varunsontakke80/Jal-Rakshak-Project-Arduino-UNO-Q/Images/Jal_Rakshak_Master_Node_Code_Flowchart.jpg

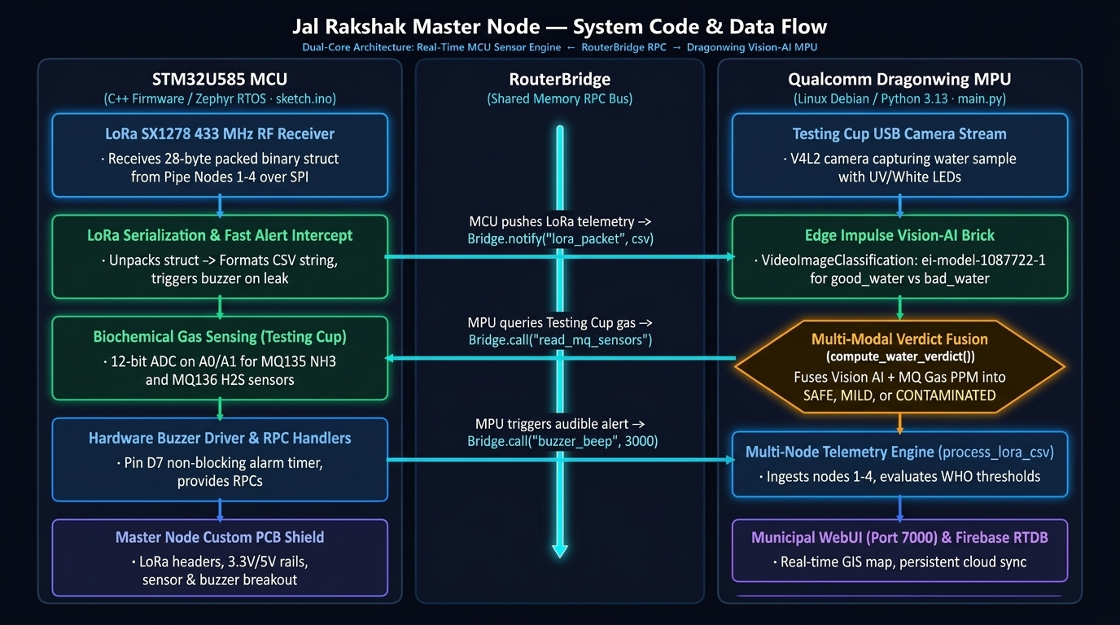
Images/Jal_Rakshak_Master_Node_Code_Flowchart.jpg
