varunsontakke80/Jal-Rakshak-Project-Arduino-UNO-Q/Images/JR1.jpeg

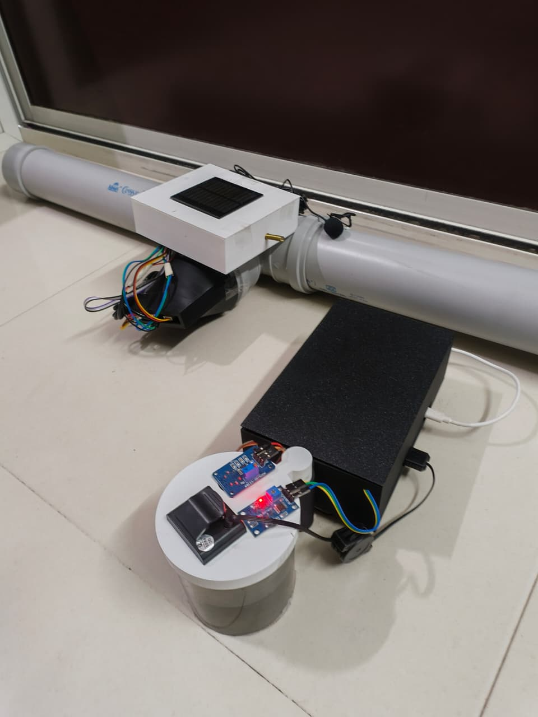
Images/JR1.jpeg
