varunsontakke80/Jal-Rakshak-Project-Arduino-UNO-Q/Images/JR2.jpeg

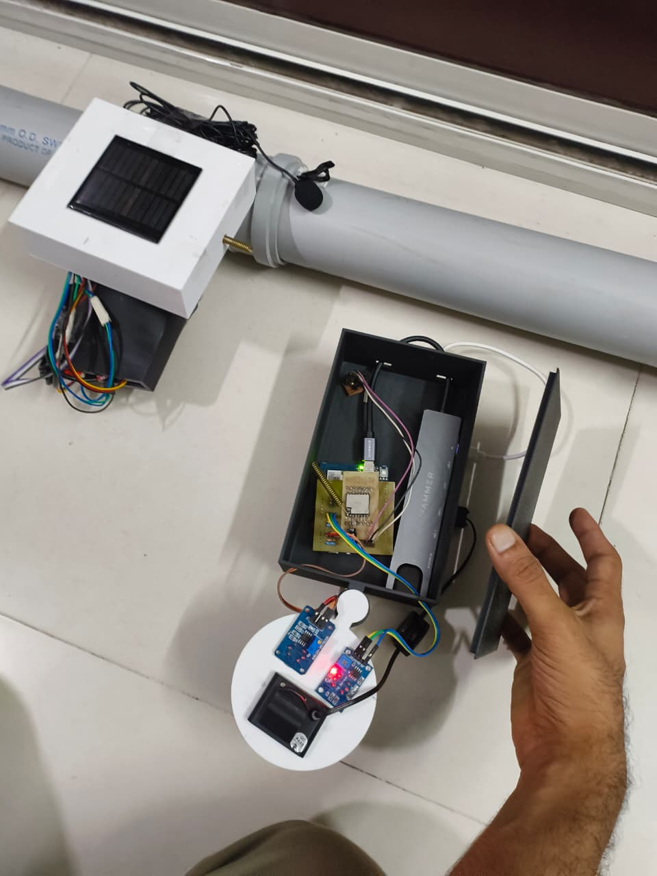
Images/JR2.jpeg
