varunsontakke80/Jal-Rakshak-Project-Arduino-UNO-Q/Images/JR3.jpeg

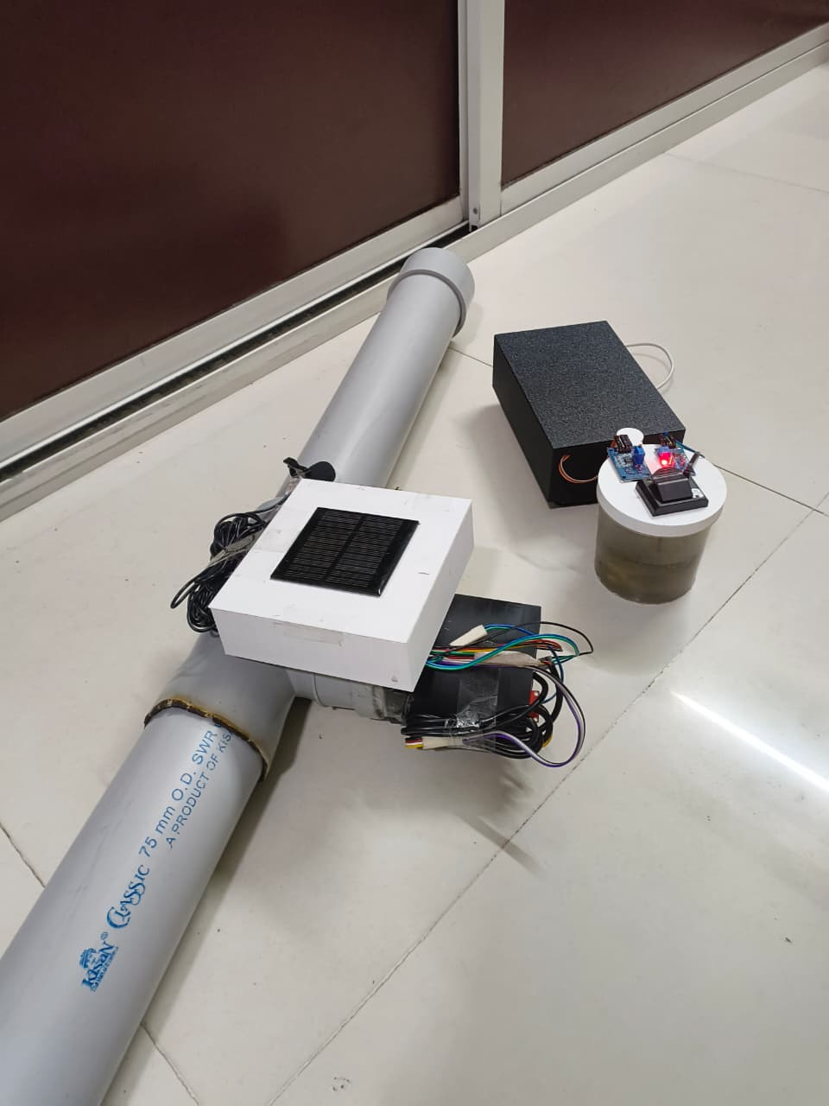
Images/JR3.jpeg
