varunsontakke80/Jal-Rakshak-Project-Arduino-UNO-Q/Images/JR4.jpeg

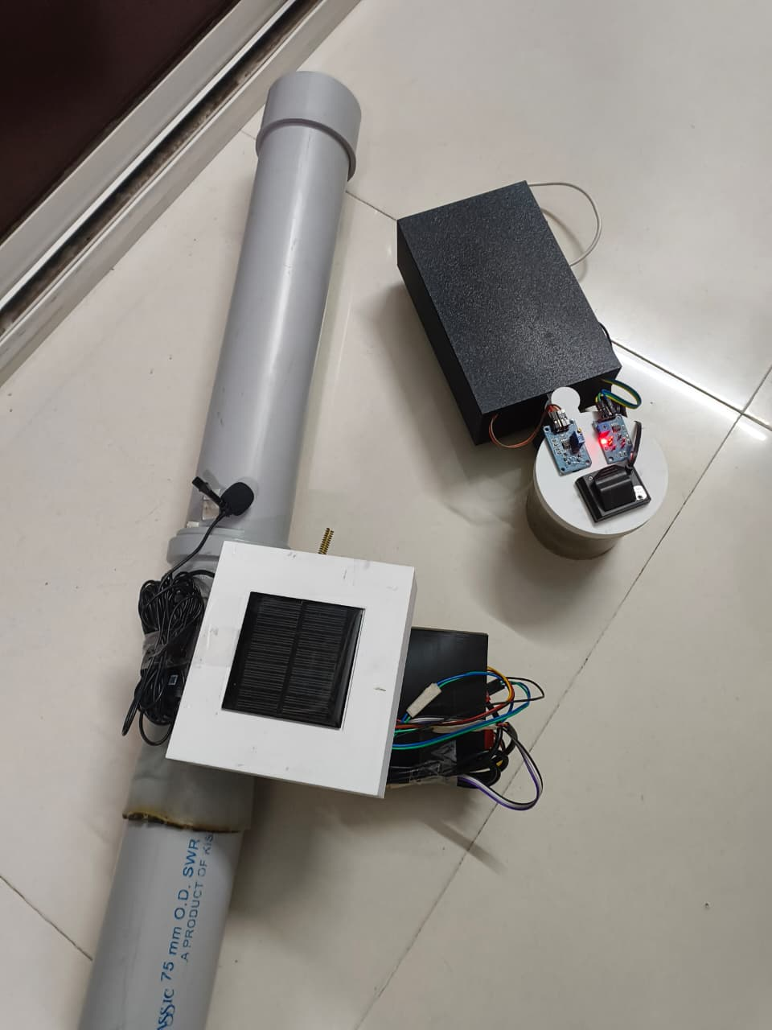
Images/JR4.jpeg
