varunsontakke80/Jal-Rakshak-Project-Arduino-UNO-Q/Images/JR5.jpeg

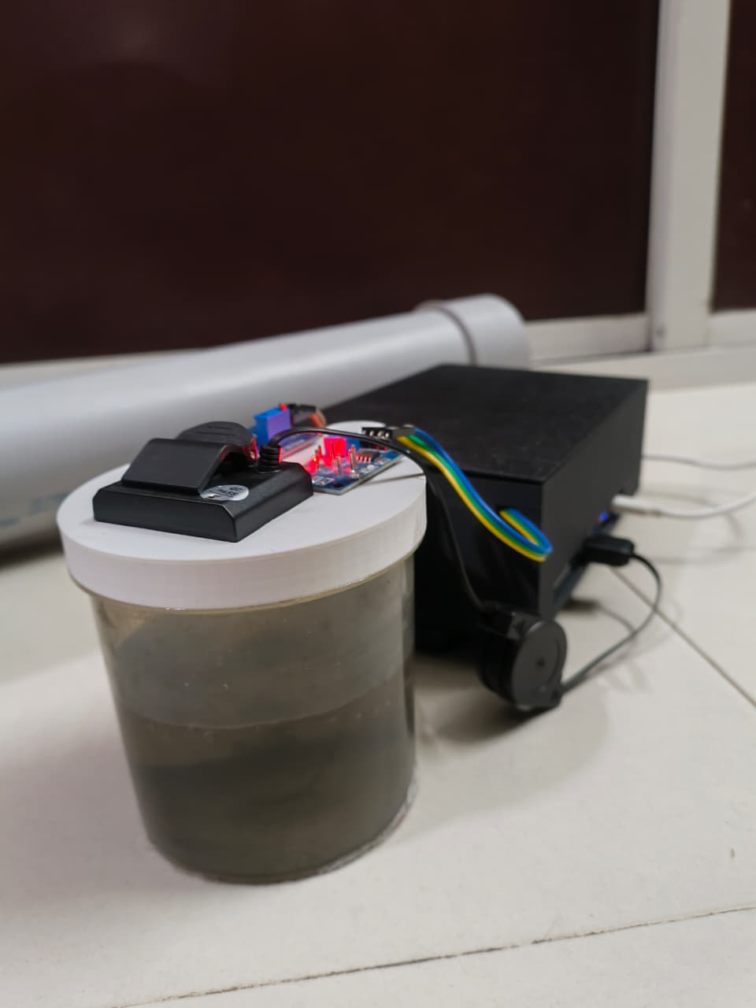
Images/JR5.jpeg
