varunsontakke80/Jal-Rakshak-Project-Arduino-UNO-Q/Images/JR6.jpeg

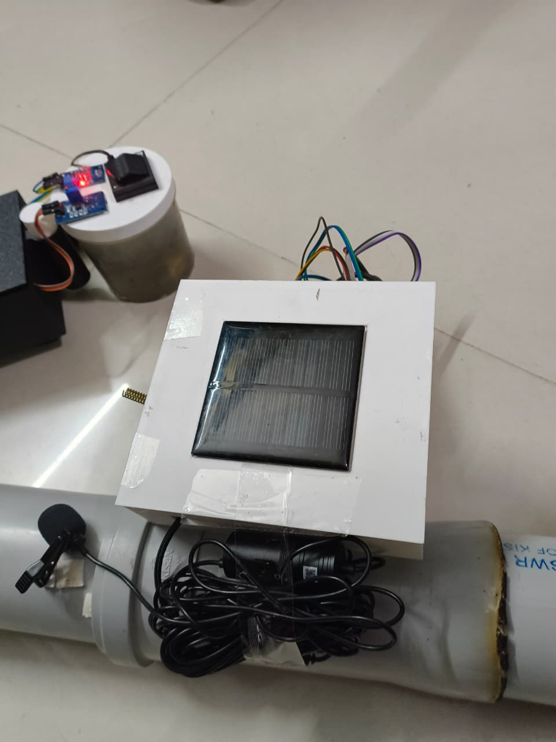
Images/JR6.jpeg
