varunsontakke80/Jal-Rakshak-Project-Arduino-UNO-Q/Images/JR7.jpeg

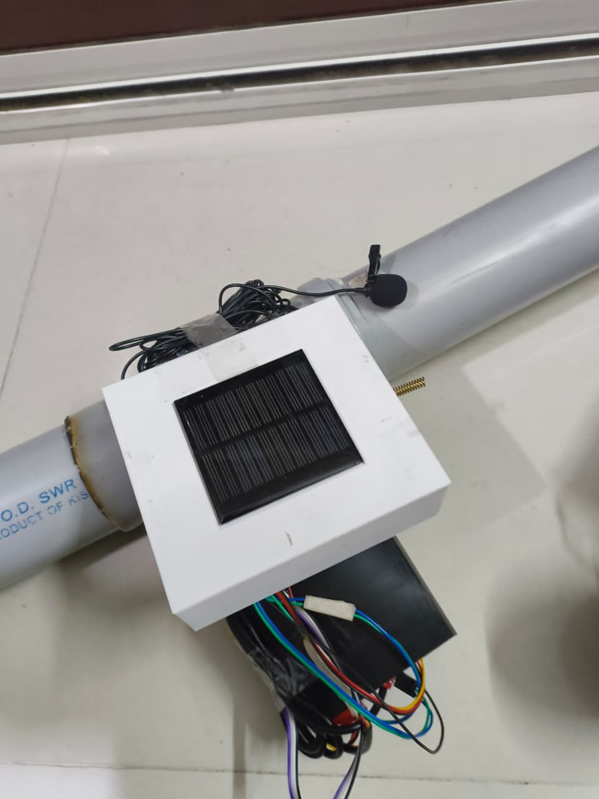
Images/JR7.jpeg
