varunsontakke80/Jal-Rakshak-Project-Arduino-UNO-Q/Images/JR8.jpeg

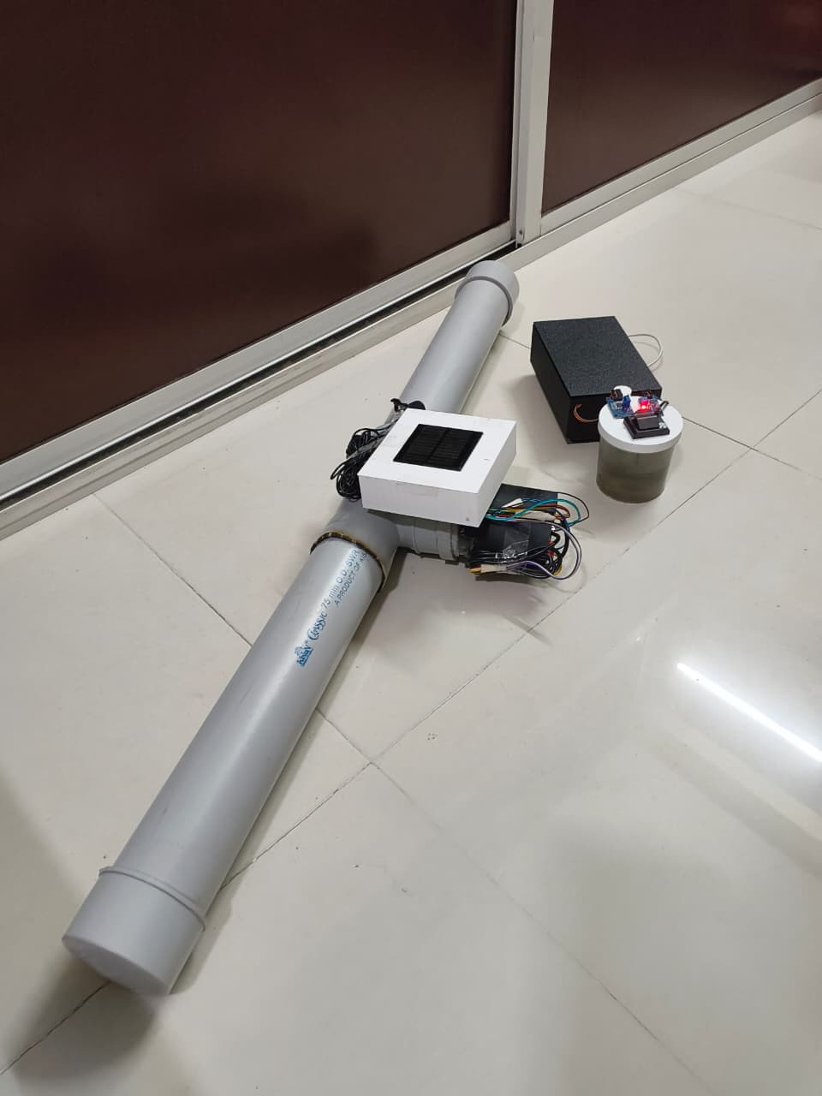
Images/JR8.jpeg
