varunsontakke80/Jal-Rakshak-Project-Arduino-UNO-Q/Images/Usb C hub.png

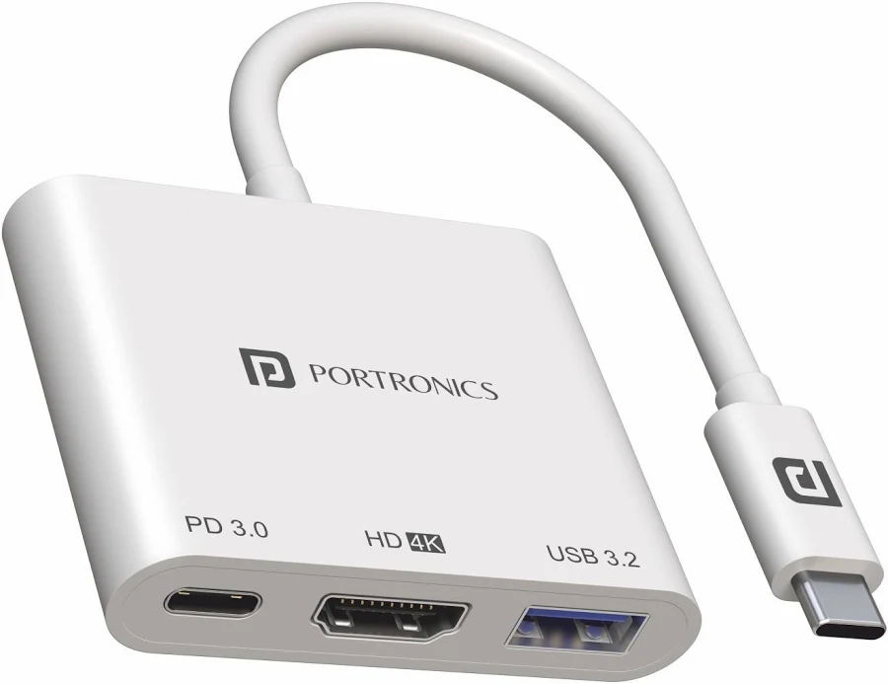
Images/Usb C hub.png
