varunsontakke80/Jal-Rakshak-Project-Arduino-UNO-Q/Images/USBc Mic.png

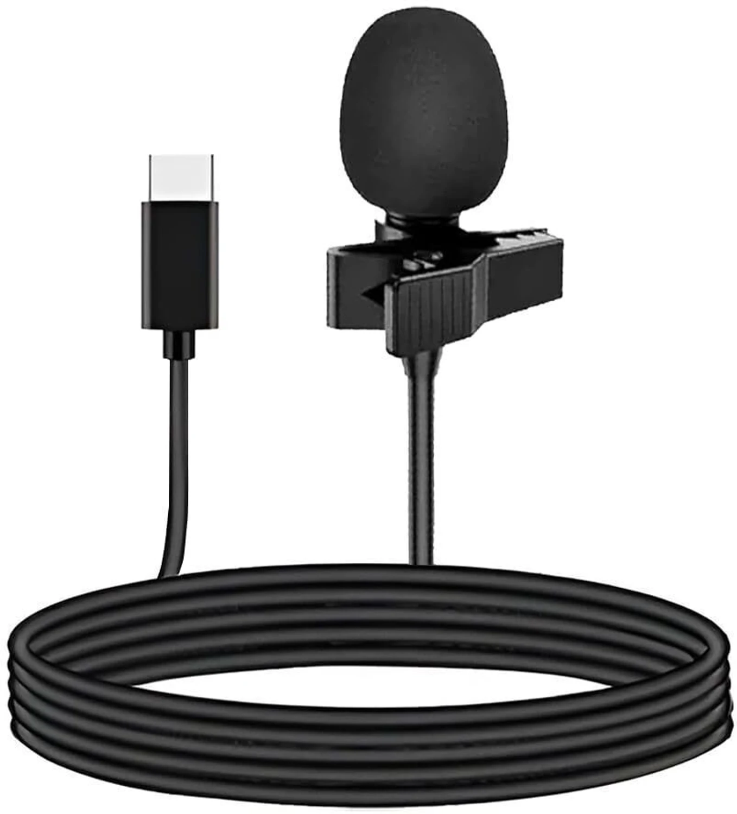
Images/USBc Mic.png
