varunsontakke80/Jal-Rakshak-Project-Arduino-UNO-Q/Master Node/CAD Files/Master Node CAD image.png

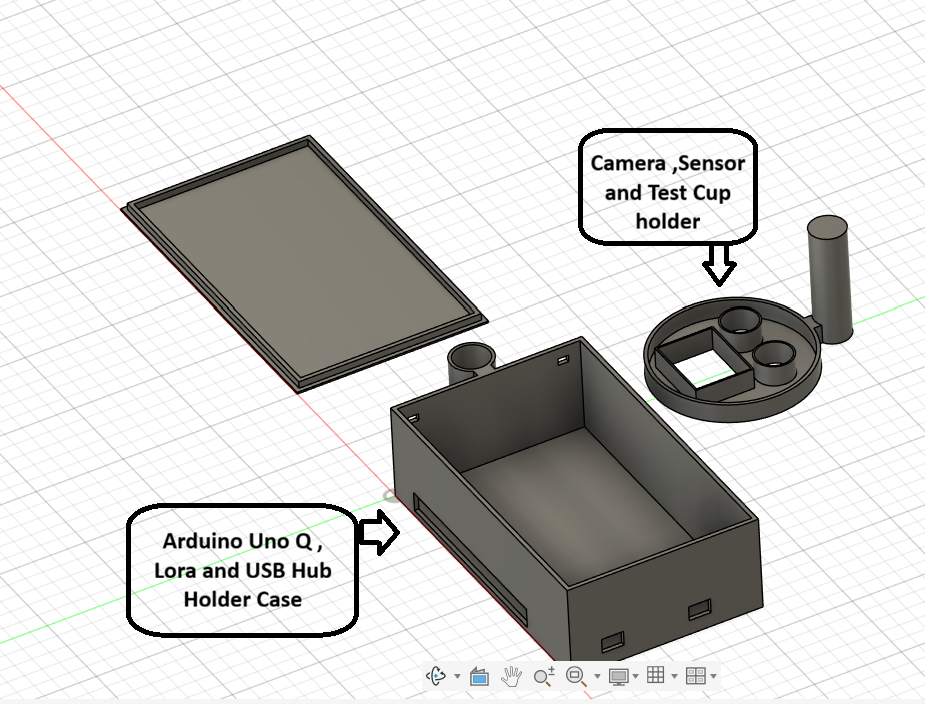
Master Node/CAD Files/Master Node CAD image.png
