varunsontakke80/Jal-Rakshak-Project-Arduino-UNO-Q/Master Node/CAD Files/Slicing SS1.png

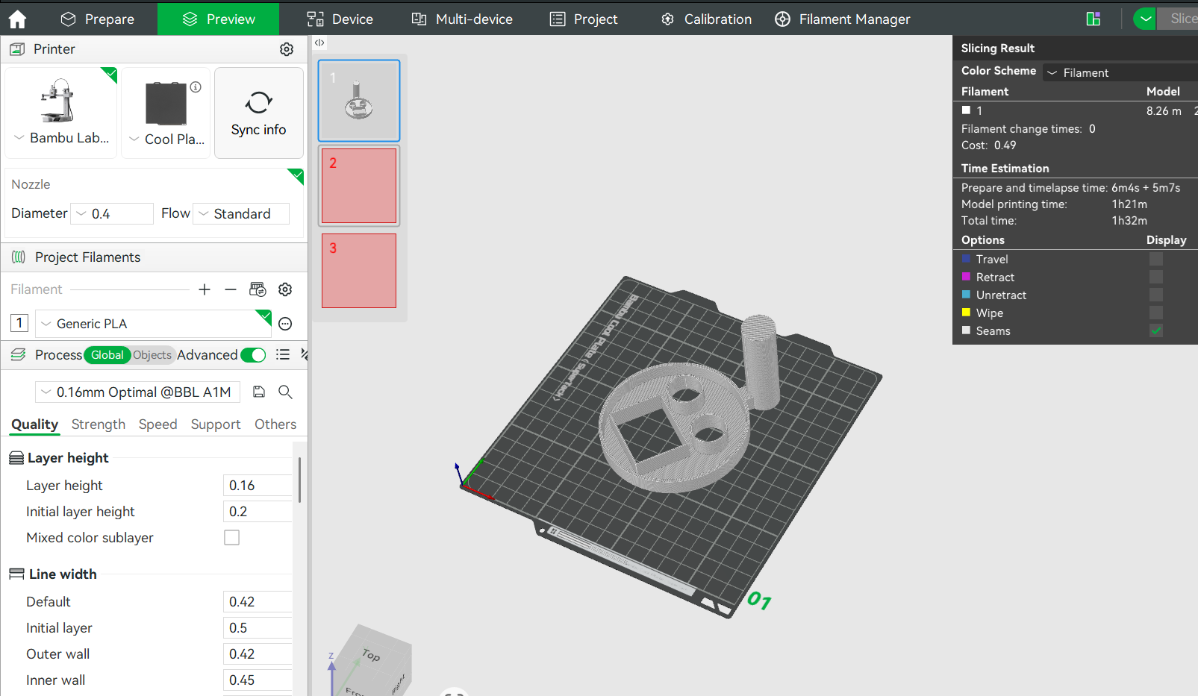
Master Node/CAD Files/Slicing SS1.png
