varunsontakke80/Jal-Rakshak-Project-Arduino-UNO-Q/Master Node/CAD Files/Slicing SS2.png

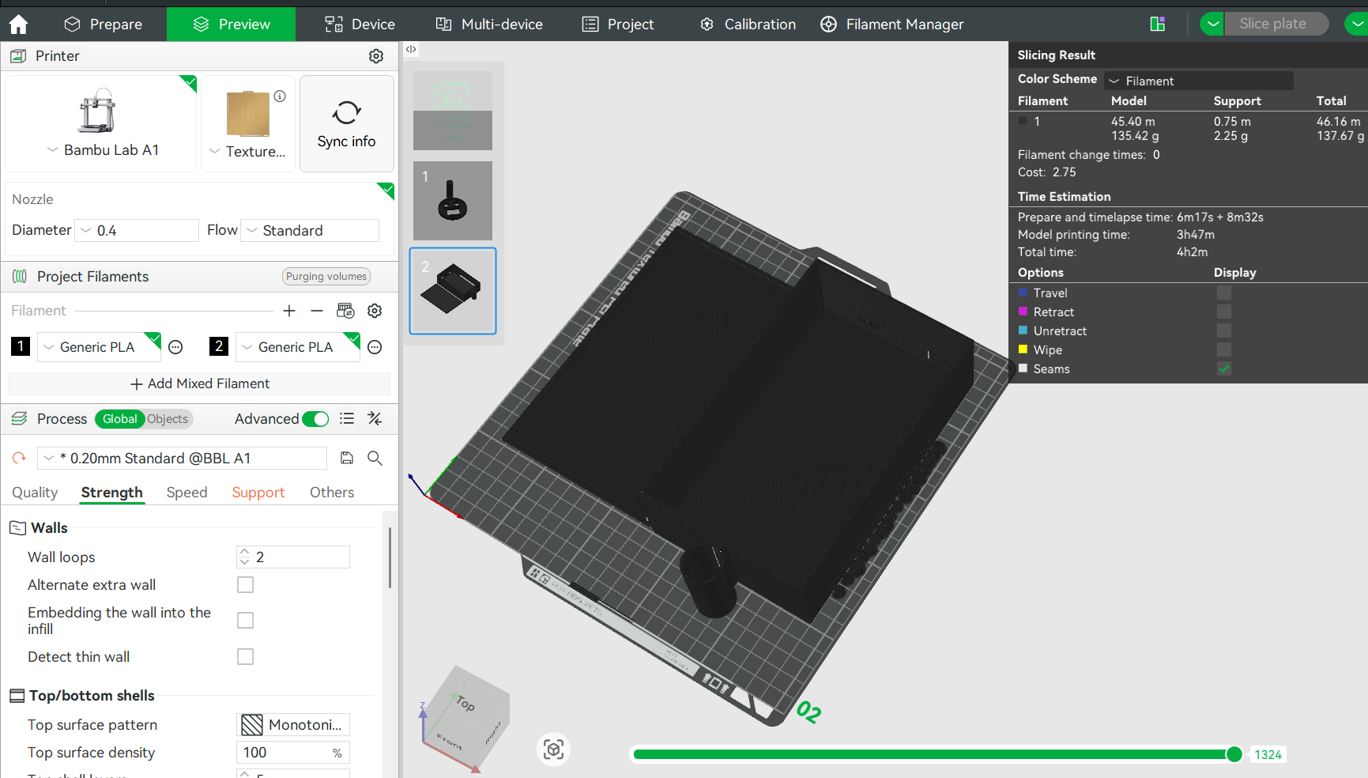
Master Node/CAD Files/Slicing SS2.png
