varunsontakke80/Jal-Rakshak-Project-Arduino-UNO-Q/Master Node/PCB Files/PCB_Jal Rakshak Master node.png

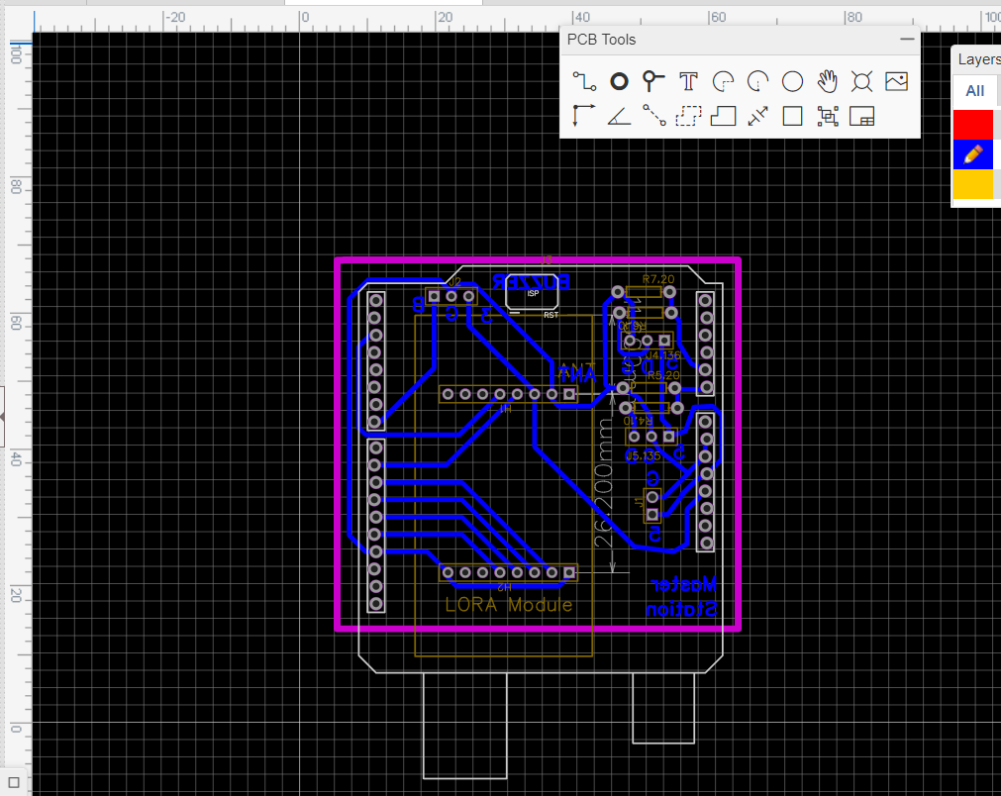
Master Node/PCB Files/PCB_Jal Rakshak Master node.png
