varunsontakke80/Jal-Rakshak-Project-Arduino-UNO-Q/Master Node/PCB Files/Schematic_Jal-Rakshak-Master-Node_2026-09-11.png

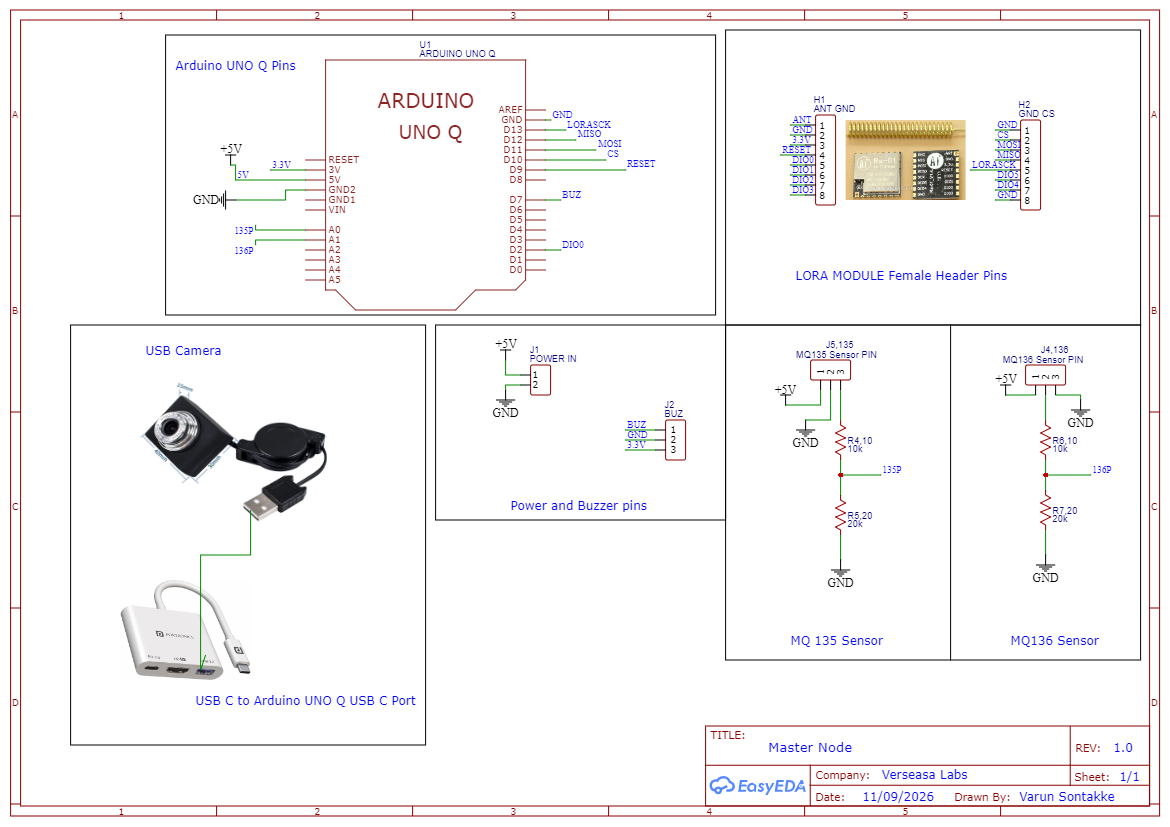
Master Node/PCB Files/Schematic_Jal-Rakshak-Master-Node_2026-09-11.png
