varunsontakke80/Jal-Rakshak-Project-Arduino-UNO-Q/Pipe Node/CAD Files/Pipe node Case .png

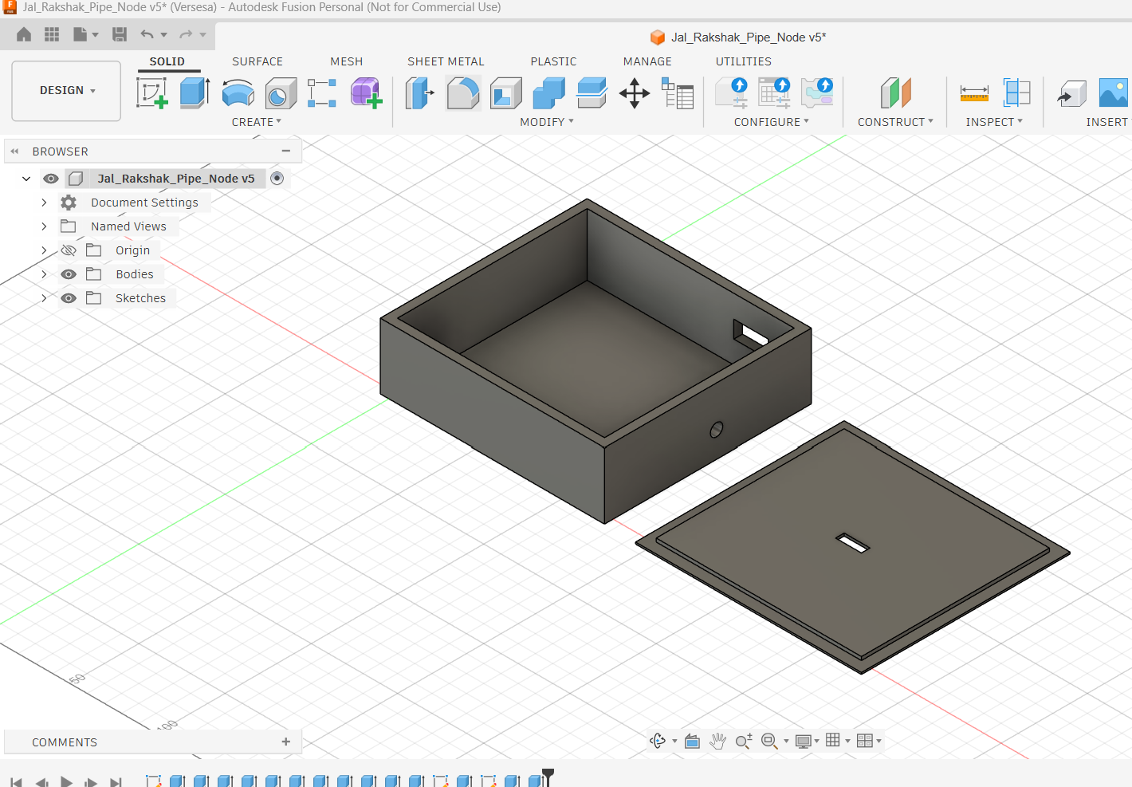
Pipe Node/CAD Files/Pipe node Case .png
