varunsontakke80/Jal-Rakshak-Project-Arduino-UNO-Q/Pipe Node/CAD Files/Pipe Node Sensor Case.png

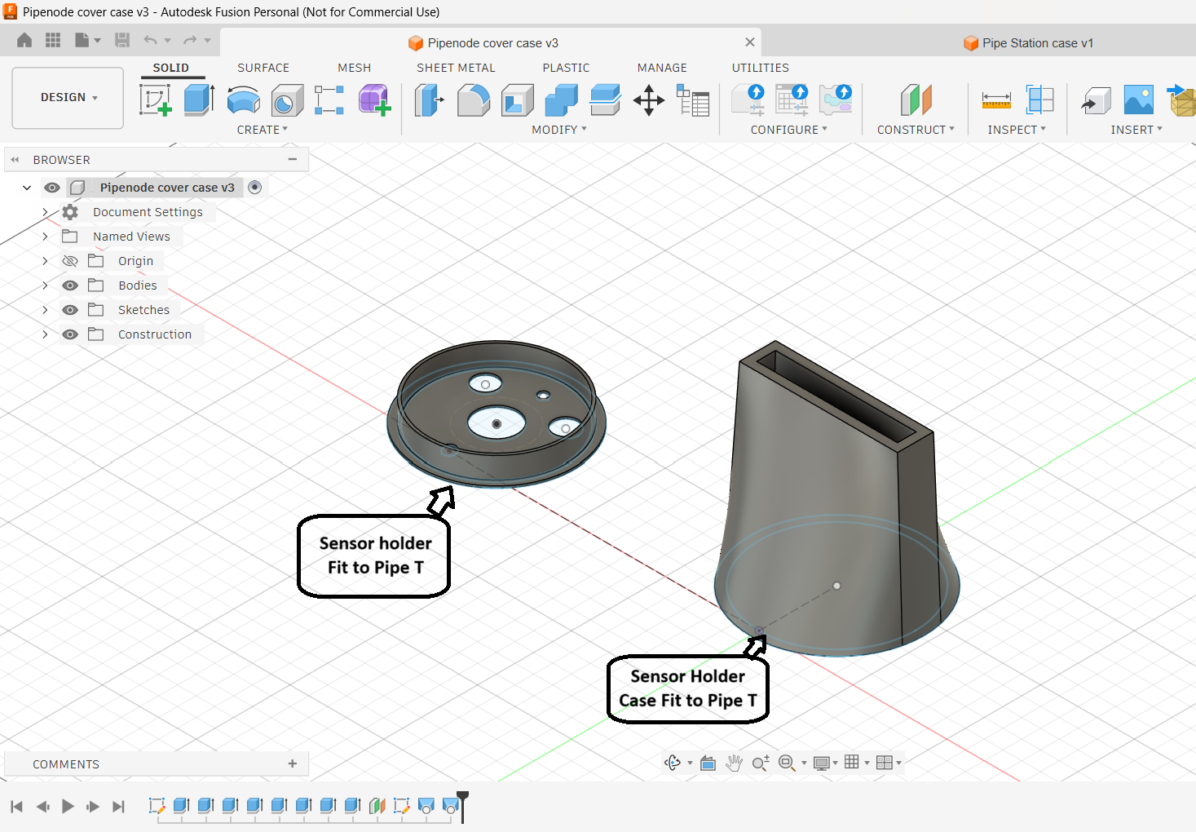
Pipe Node/CAD Files/Pipe Node Sensor Case.png
