varunsontakke80/Jal-Rakshak-Project-Arduino-UNO-Q/Pipe Node/CAD Files/Slicing SS 2.png

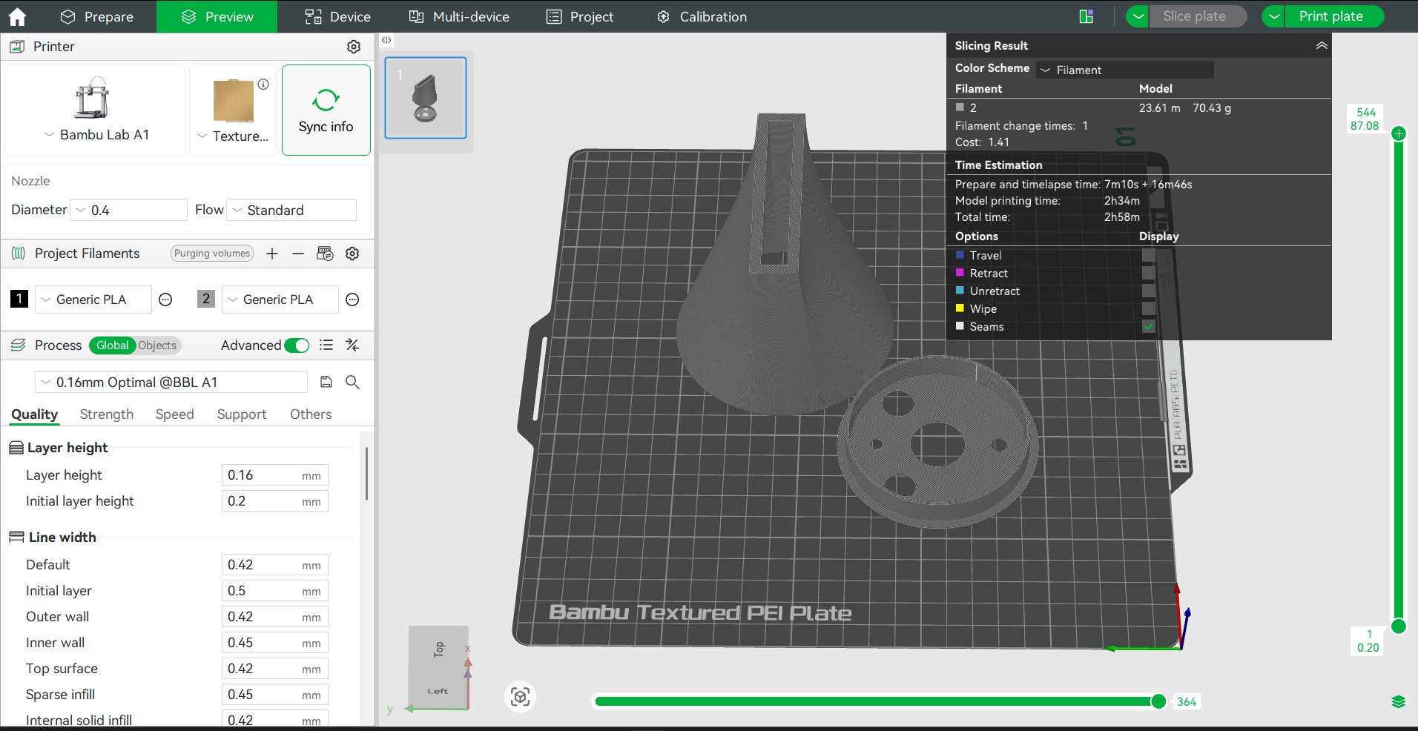
Pipe Node/CAD Files/Slicing SS 2.png
