varunsontakke80/Jal-Rakshak-Project-Arduino-UNO-Q/Pipe Node/PCB Files/Schematic_Jal-Rakshak-Pipe-Node_2026-09-11.png

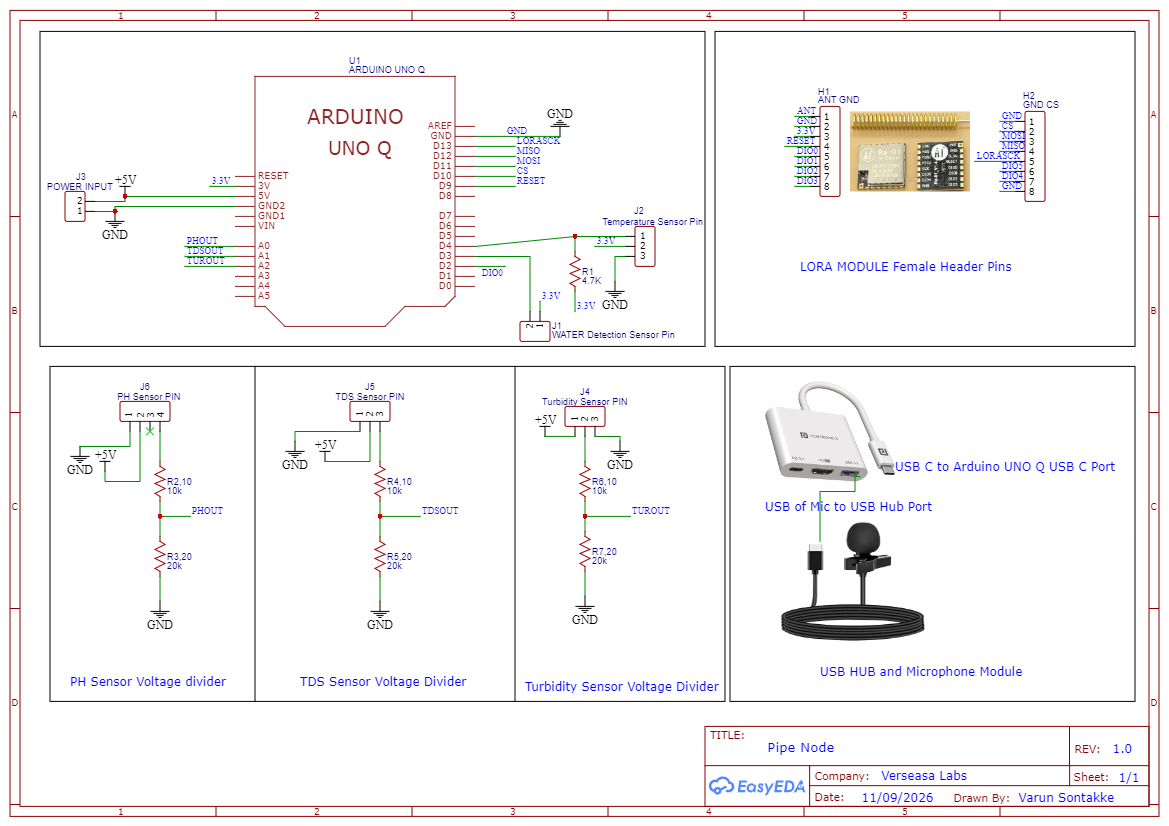
Pipe Node/PCB Files/Schematic_Jal-Rakshak-Pipe-Node_2026-09-11.png
