varunsontakke80/Jal-Rakshak-Project-Arduino-UNO-Q/Pipe Node/PCB Files/Sensor PCB Back.jpg

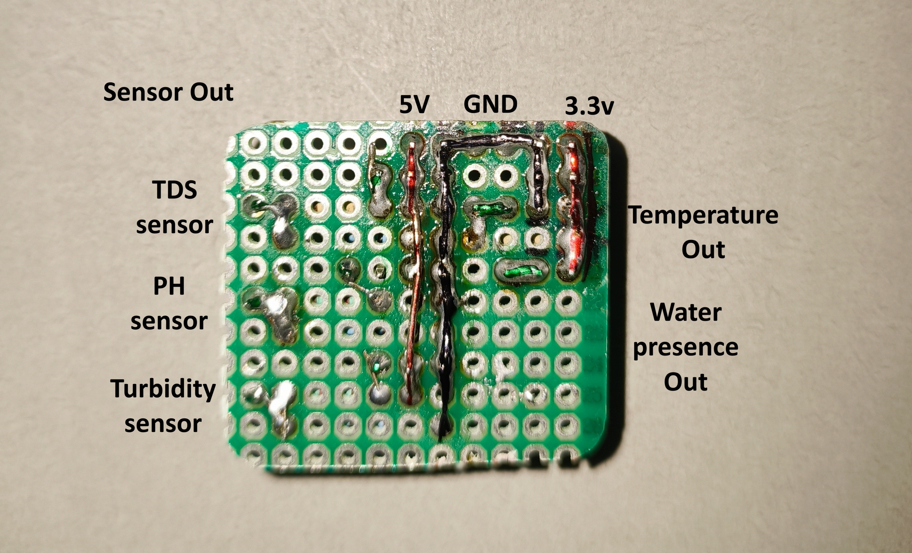
Pipe Node/PCB Files/Sensor PCB Back.jpg
