varunsontakke80/Jal-Rakshak-Project-Arduino-UNO-Q/Pipe Node/PCB Files/Sensor PCB Front.jpg

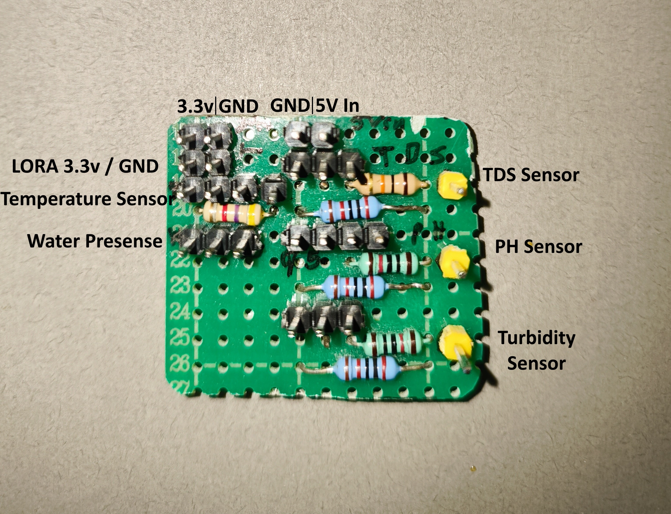
Pipe Node/PCB Files/Sensor PCB Front.jpg
