varunsontakke80/Jal-Rakshak-Project-Arduino-UNO-Q/Pipe Node/Pipe Node Componenets.jpeg

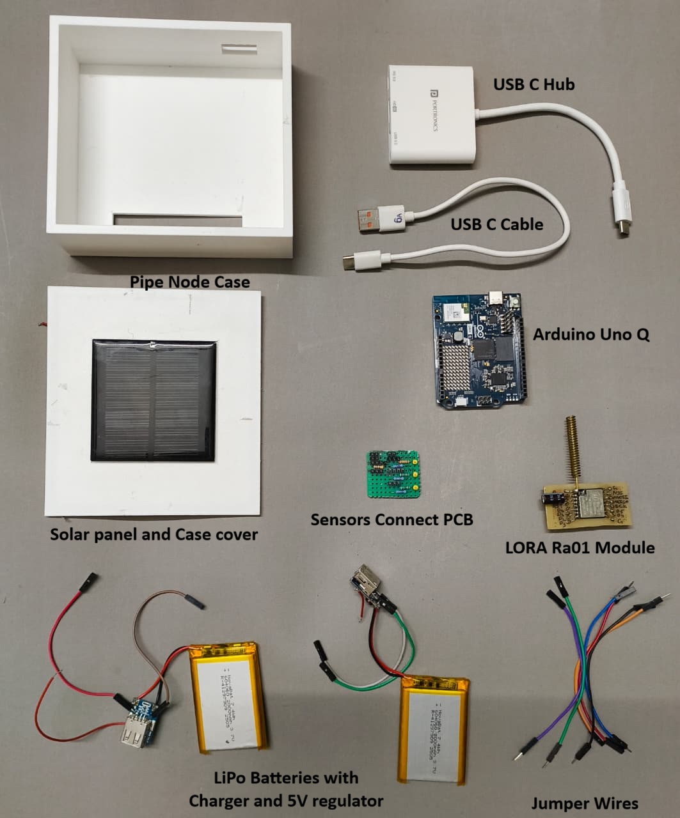
Pipe Node/Pipe Node Componenets.jpeg
