varunsontakke80/Jal-Rakshak-Project-Arduino-UNO-Q/Pipe Node/Pipe Node sensors.jpeg

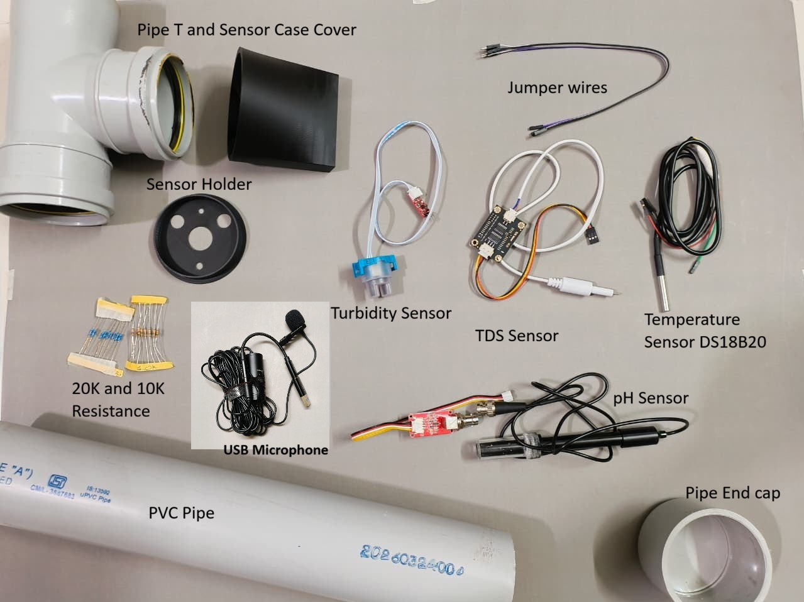
Pipe Node/Pipe Node sensors.jpeg
