varunsontakke80/Jal-Rakshak-Project-Arduino-UNO-Q/Master Node/Master Node components.jpeg

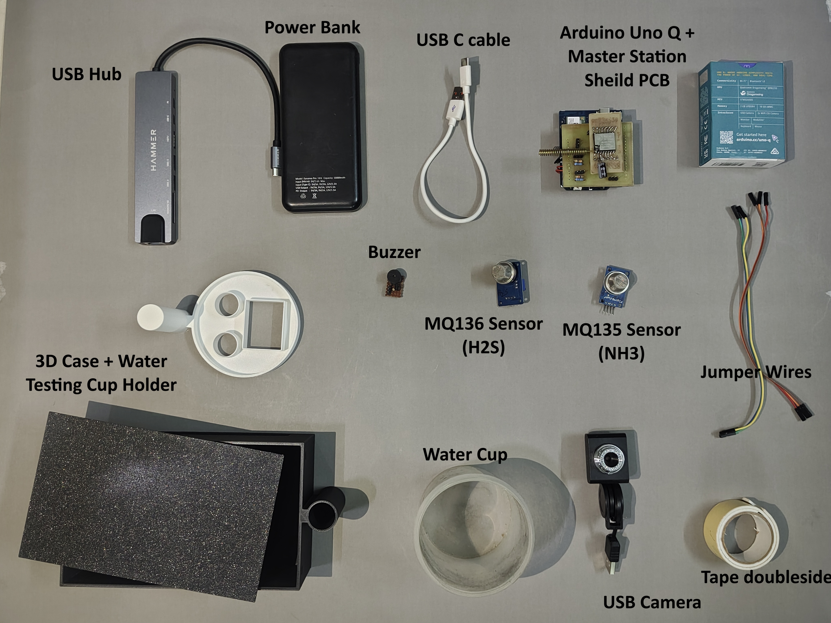
Master Node/Master Node components.jpeg
