varunsontakke80/Jal-Rakshak-Project-Arduino-UNO-Q/Master Node/Steps to assembly/2.jpeg

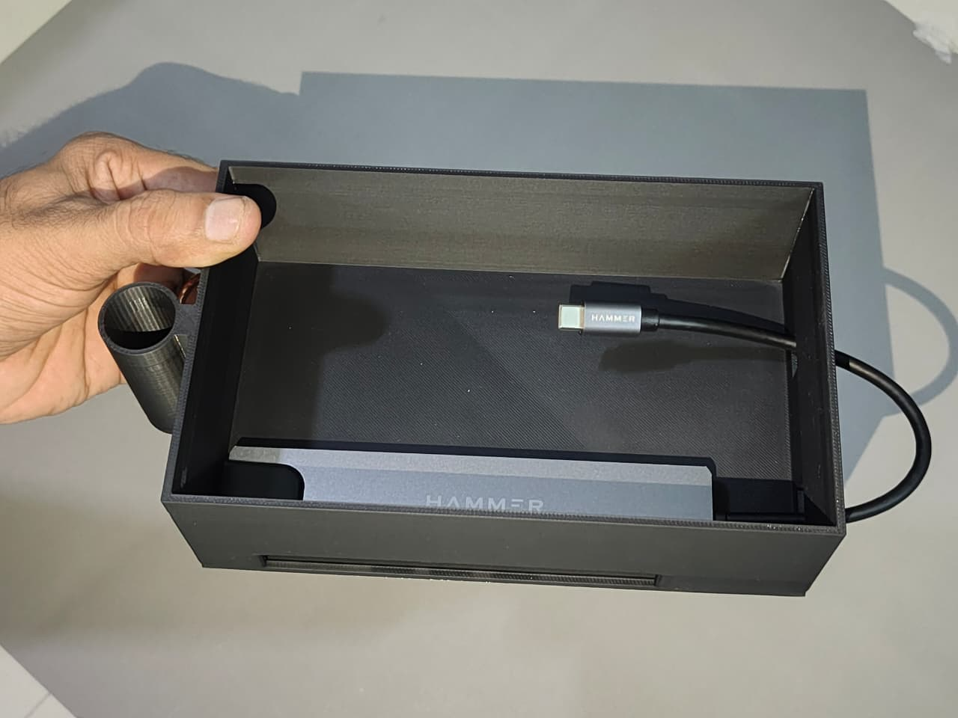
Master Node/Steps to assembly/2.jpeg
