varunsontakke80/Jal-Rakshak-Project-Arduino-UNO-Q/Master Node/Steps to assembly/3.jpeg

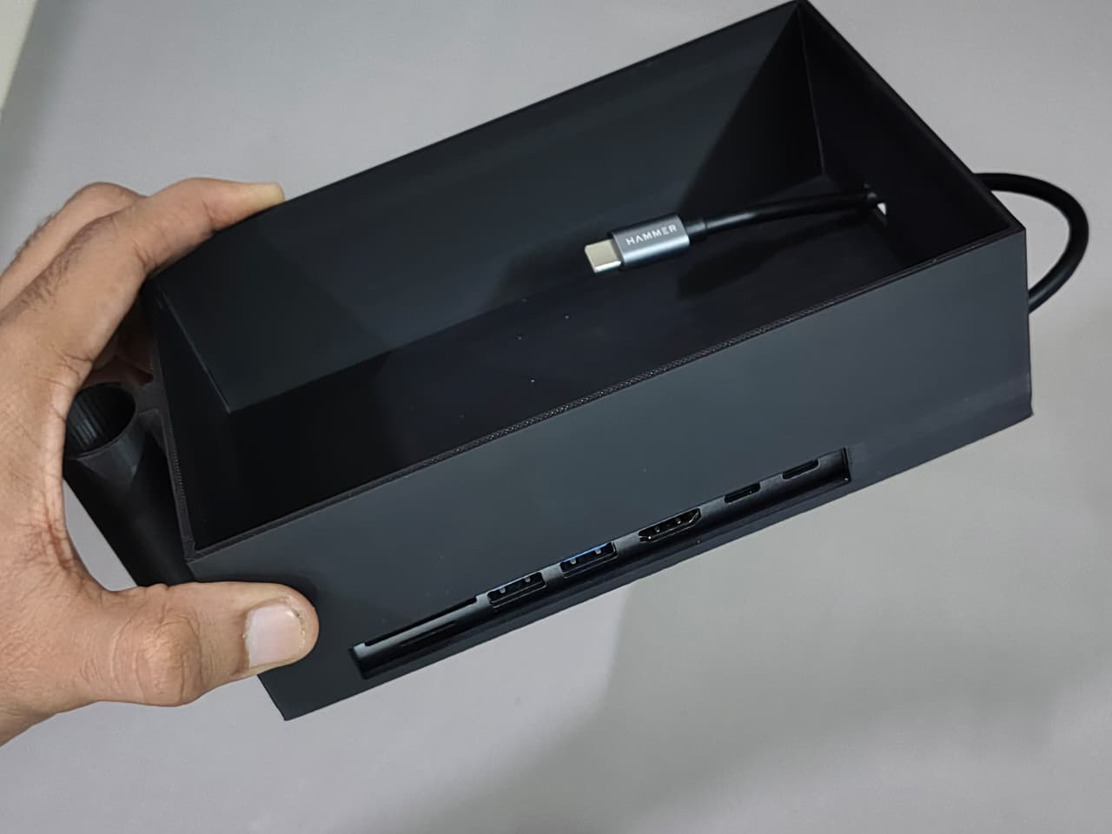
Master Node/Steps to assembly/3.jpeg
