varunsontakke80/Jal-Rakshak-Project-Arduino-UNO-Q/Master Node/Steps to assembly/4.jpeg

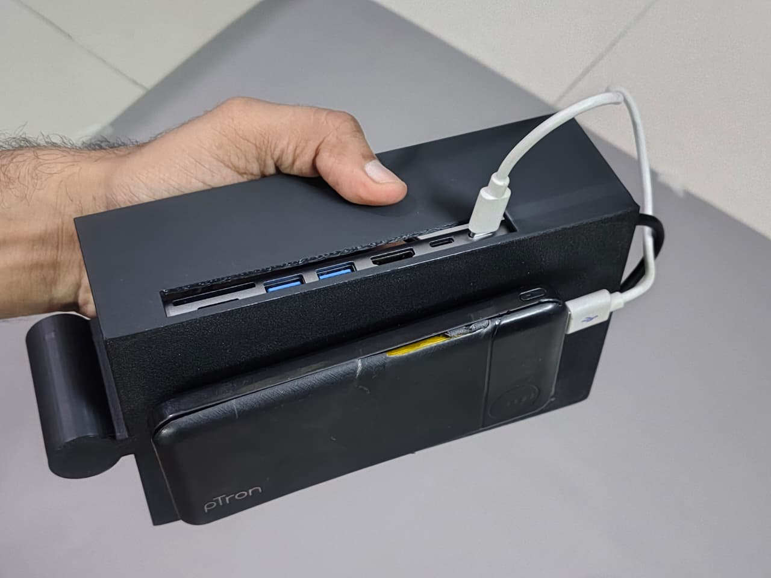
Master Node/Steps to assembly/4.jpeg
