varunsontakke80/Jal-Rakshak-Project-Arduino-UNO-Q/Master Node/Steps to assembly/5.jpeg

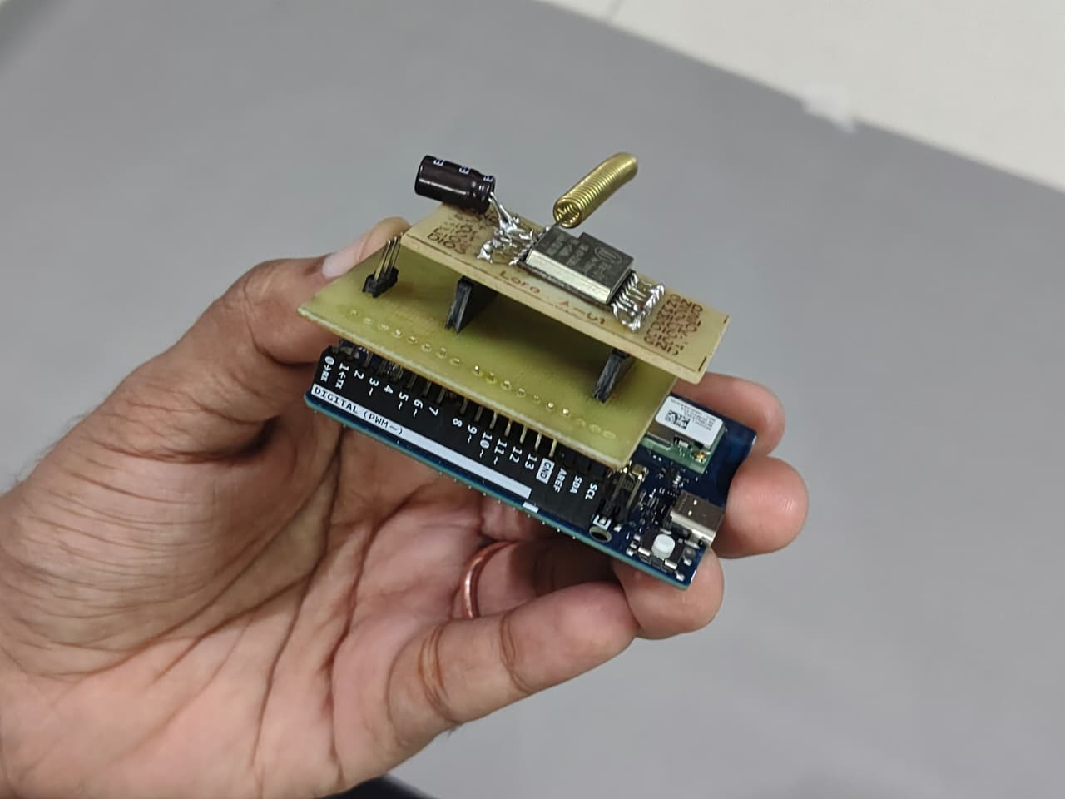
Master Node/Steps to assembly/5.jpeg
