varunsontakke80/Jal-Rakshak-Project-Arduino-UNO-Q/Master Node/Steps to assembly/7.jpeg

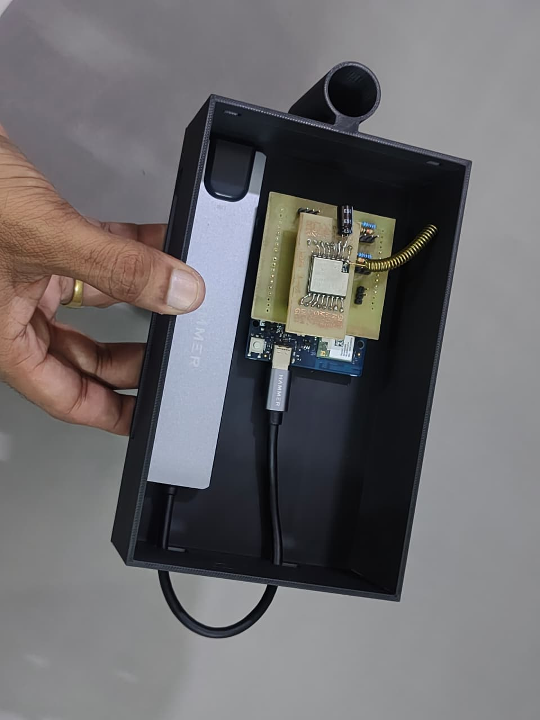
Master Node/Steps to assembly/7.jpeg
