varunsontakke80/Jal-Rakshak-Project-Arduino-UNO-Q/Master Node/Steps to assembly/10.jpeg

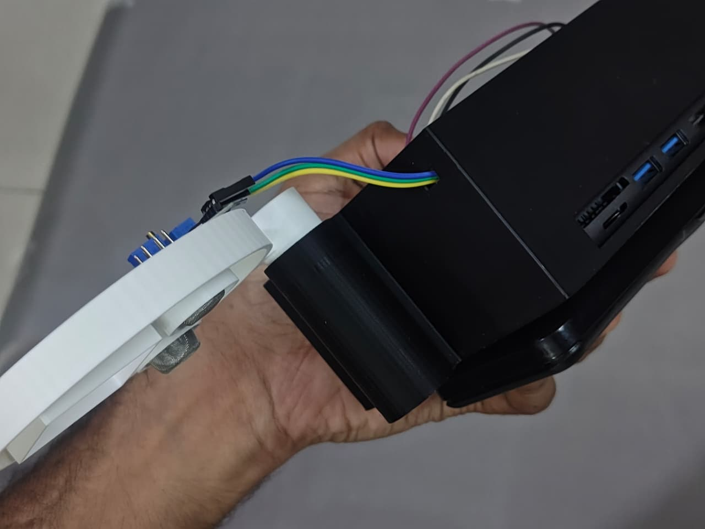
Master Node/Steps to assembly/10.jpeg
