varunsontakke80/Jal-Rakshak-Project-Arduino-UNO-Q/Master Node/Steps to assembly/14.jpeg

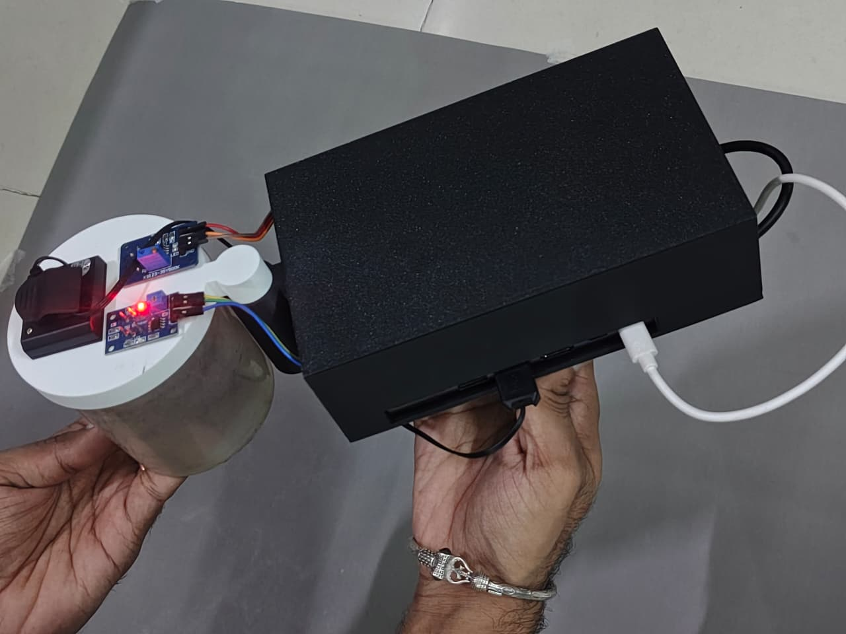
Master Node/Steps to assembly/14.jpeg
