varunsontakke80/Jal-Rakshak-Project-Arduino-UNO-Q/Master Node/Steps to assembly/PCB1.jpeg

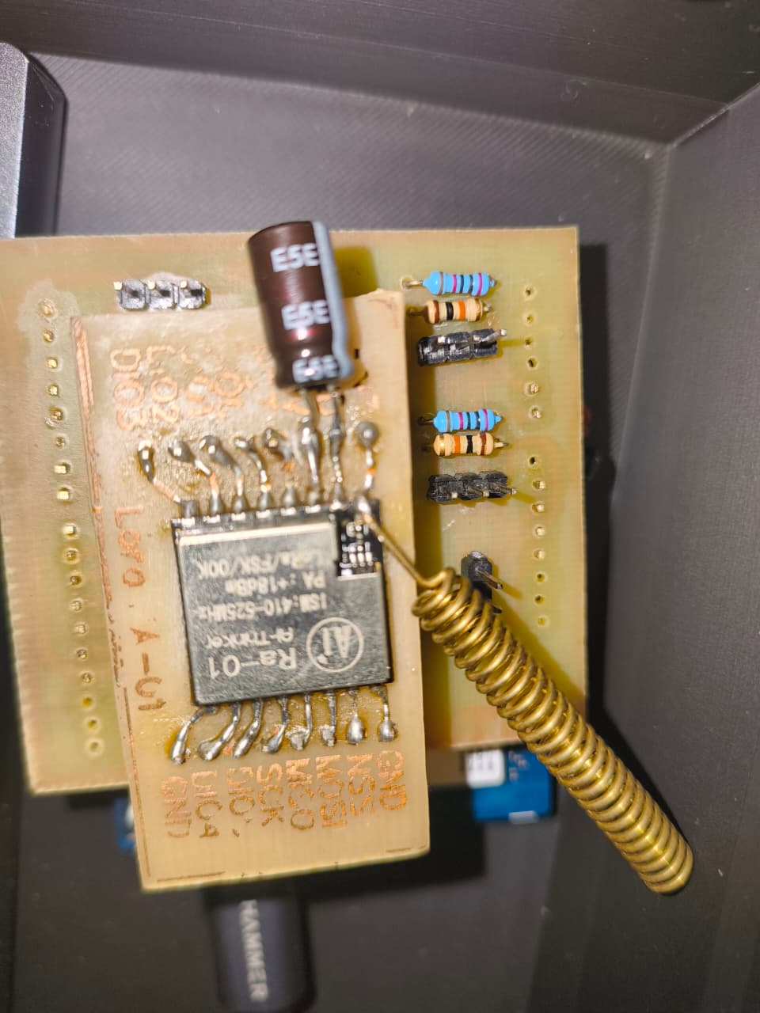
Master Node/Steps to assembly/PCB1.jpeg
