varunsontakke80/Jal-Rakshak-Project-Arduino-UNO-Q/Master Node/Steps to assembly/PCB.jpeg

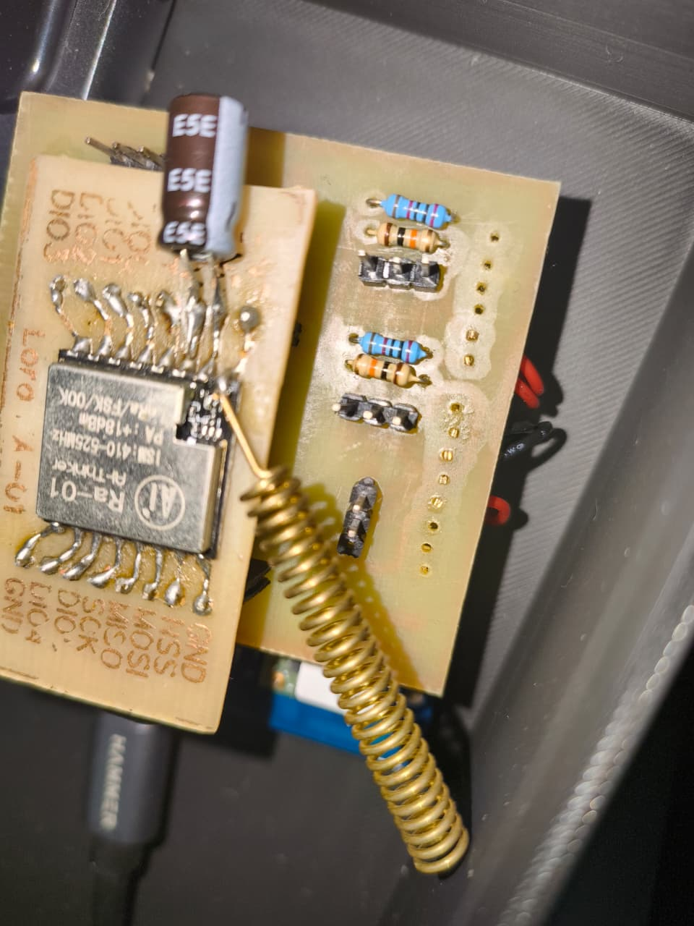
Master Node/Steps to assembly/PCB.jpeg
