varunsontakke80/Jal-Rakshak-Project-Arduino-UNO-Q/Pipe Node/Steps to assembly/13.jpeg

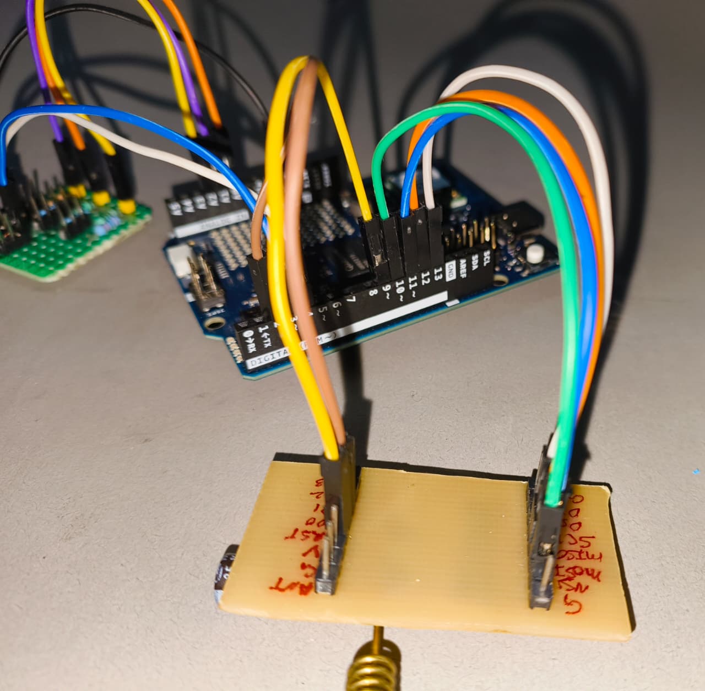
Pipe Node/Steps to assembly/13.jpeg
