varunsontakke80/Jal-Rakshak-Project-Arduino-UNO-Q/Pipe Node/Steps to assembly/17.jpeg

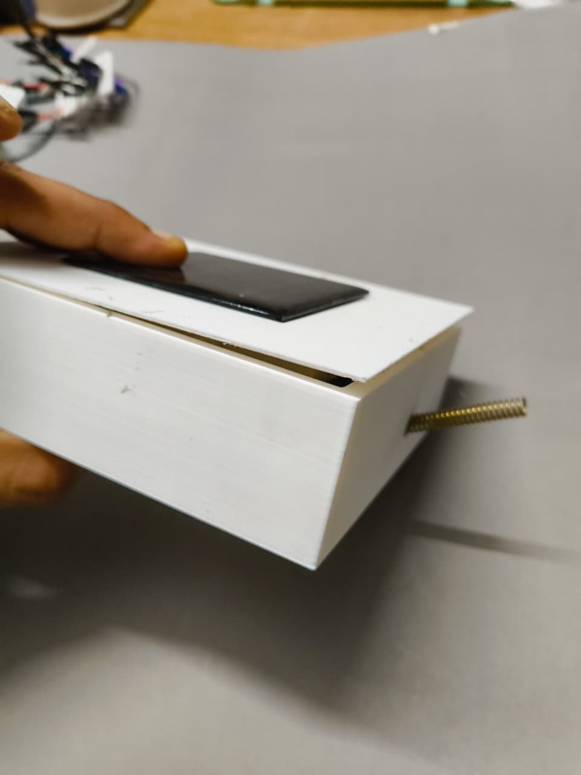
Pipe Node/Steps to assembly/17.jpeg
