varunsontakke80/Jal-Rakshak-Project-Arduino-UNO-Q/Pipe Node/Steps to assembly/18.jpeg

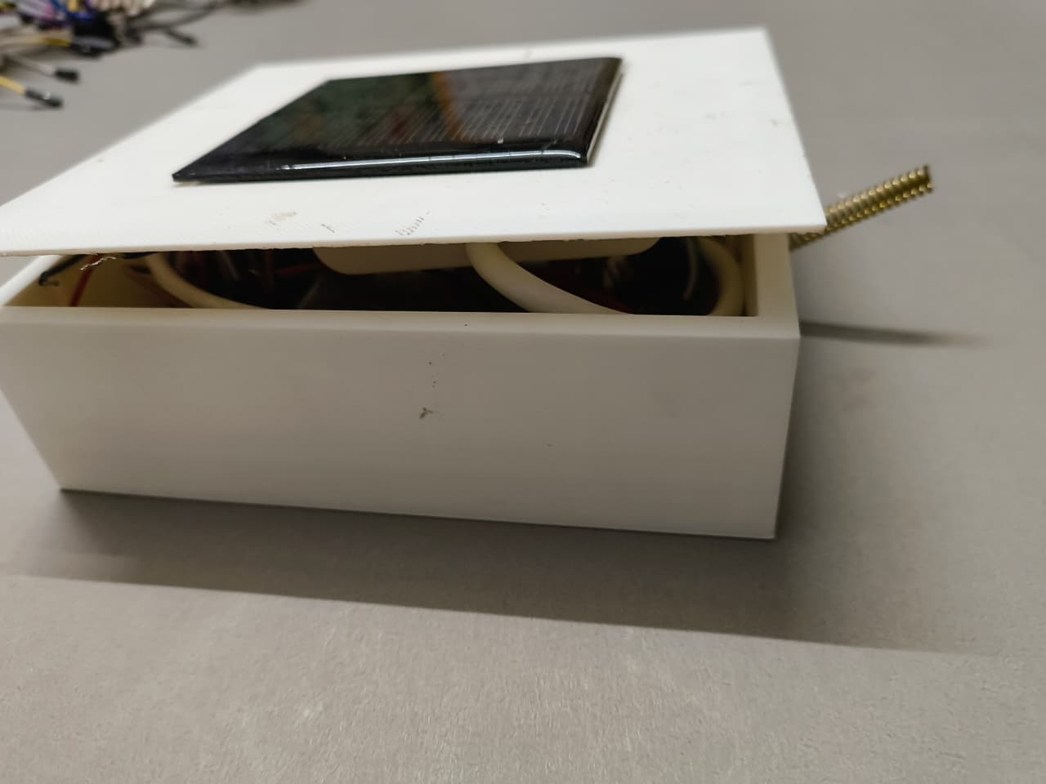
Pipe Node/Steps to assembly/18.jpeg
