varunsontakke80/Jal-Rakshak-Project-Arduino-UNO-Q/Pipe Node/Steps to assembly/EdgeAI1.jpeg

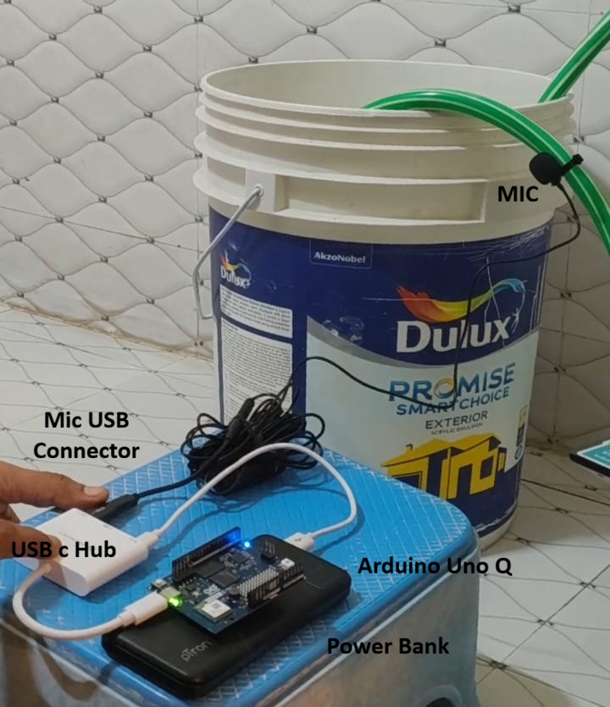
Pipe Node/Steps to assembly/EdgeAI1.jpeg
