varunsontakke80/Jal-Rakshak-Project-Arduino-UNO-Q/Pipe Node/Steps to assembly/EdgeAi3.jpeg

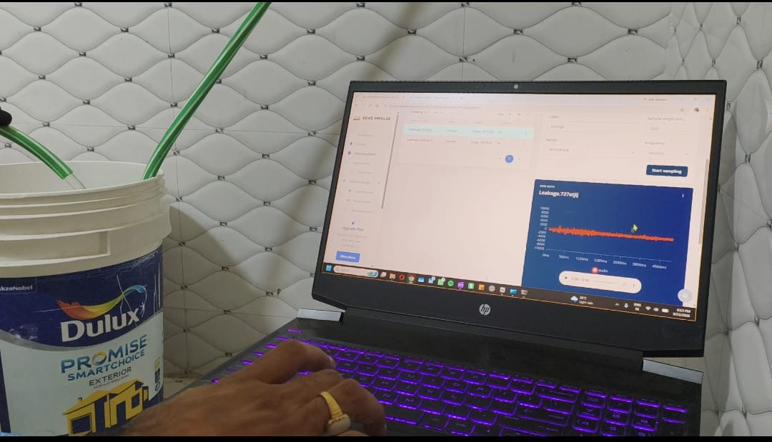
Pipe Node/Steps to assembly/EdgeAi3.jpeg
