varunsontakke80/Jal-Rakshak-Project-Arduino-UNO-Q/Pipe Node/Steps to assembly/EdgeAI4.jpeg

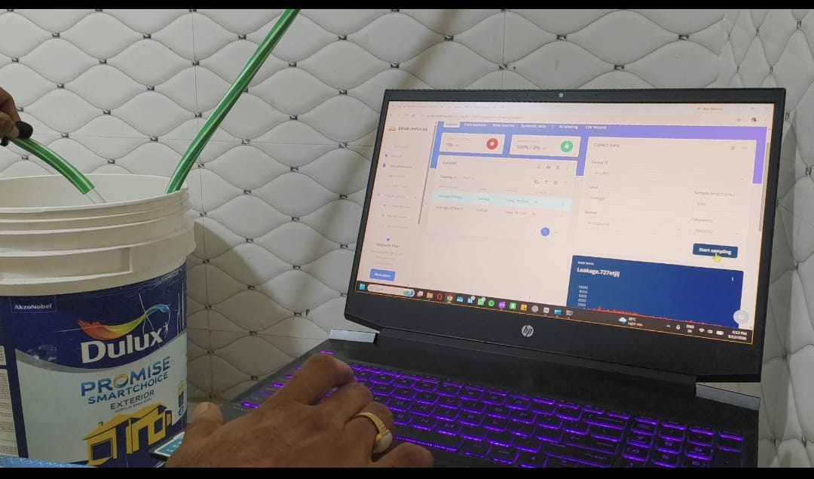
Pipe Node/Steps to assembly/EdgeAI4.jpeg
