varunsontakke80/Jal-Rakshak-Project-Arduino-UNO-Q/Pipe Node/Steps to assembly/EdgeAI6.jpeg

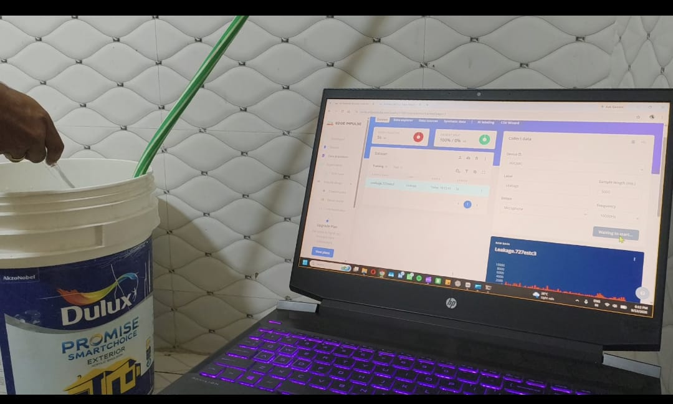
Pipe Node/Steps to assembly/EdgeAI6.jpeg
