varunsontakke80/Jal-Rakshak-Project-Arduino-UNO-Q/Pipe Node/Steps to assembly/EdgeAi 2.jpeg

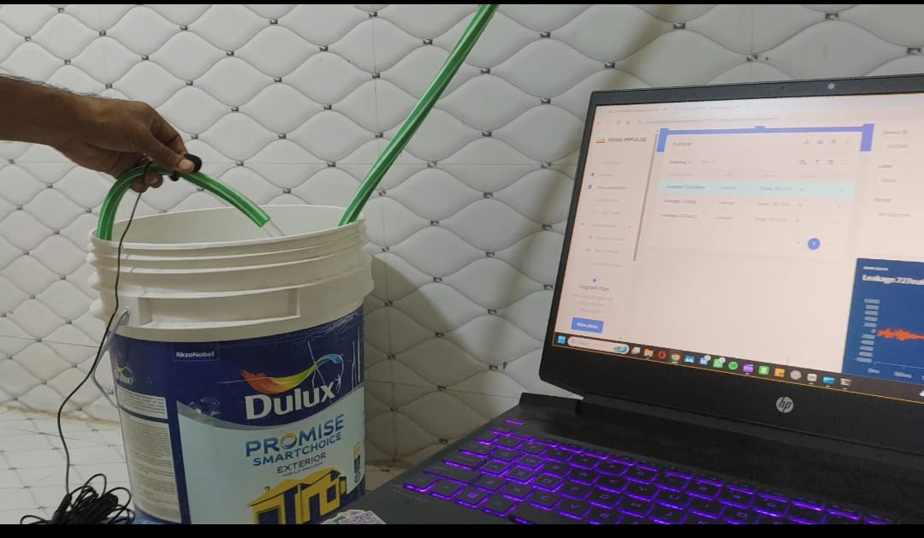
Pipe Node/Steps to assembly/EdgeAi 2.jpeg
