varunsontakke80/Jal-Rakshak-Project-Arduino-UNO-Q/Pipe Node/Steps to assembly/step 6.3.jpeg

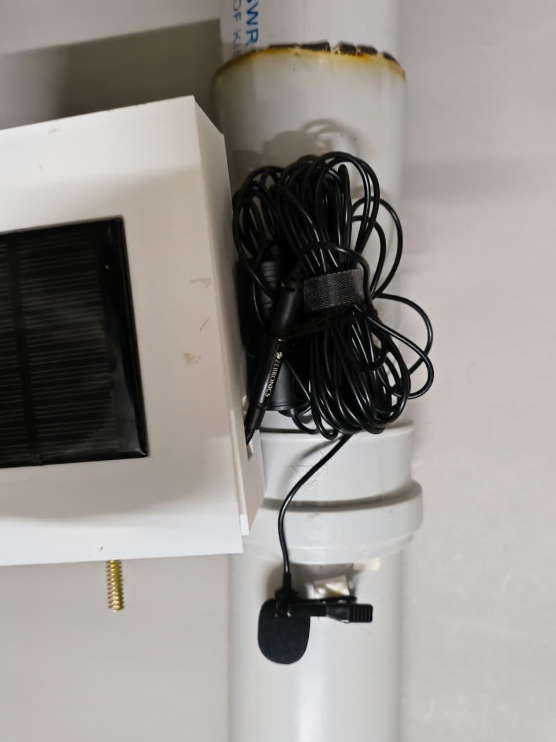
Pipe Node/Steps to assembly/step 6.3.jpeg
